he29-net/thermal-cam/3.Software/User/gd32f103c_lcd_eval.c

/*!
    \file    gd32f103c_lcd_eval.c
    \brief   LCD driver functions

    \version 2014-12-26, V1.0.0, demo for GD32F10x
    \version 2017-06-20, V2.0.0, demo for GD32F10x
    \version 2018-07-31, V2.1.0, demo for GD32F10x
*/

/*
    Copyright (c) 2018, GigaDevice Semiconductor Inc.

    All rights reserved.

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
    1. Redistributions of source code must retain the above copyright notice, this
       list of conditions and the following disclaimer.
    2. Redistributions in binary form must reproduce the above copyright notice,
       this list of conditions and the following disclaimer in the documentation
       and/or other materials provided with the distribution.
    3. Neither the name of the copyright holder nor the names of its contributors
       may be used to endorse or promote products derived from this software without
       specific prior written permission.

    THIS SOFTWARE IS PROVIDED BY THE COPYRIGHT HOLDERS AND CONTRIBUTORS "AS IS"
AND ANY EXPRESS OR IMPLIED WARRANTIES, INCLUDING, BUT NOT LIMITED TO, THE IMPLIED
WARRANTIES OF MERCHANTABILITY AND FITNESS FOR A PARTICULAR PURPOSE ARE DISCLAIMED.
IN NO EVENT SHALL THE COPYRIGHT HOLDER OR CONTRIBUTORS BE LIABLE FOR ANY DIRECT,
INDIRECT, INCIDENTAL, SPECIAL, EXEMPLARY, OR CONSEQUENTIAL DAMAGES (INCLUDING, BUT
NOT LIMITED TO, PROCUREMENT OF SUBSTITUTE GOODS OR SERVICES; LOSS OF USE, DATA, OR
PROFITS; OR BUSINESS INTERRUPTION) HOWEVER CAUSED AND ON ANY THEORY OF LIABILITY,
WHETHER IN CONTRACT, STRICT LIABILITY, OR TORT (INCLUDING NEGLIGENCE OR OTHERWISE)
ARISING IN ANY WAY OUT OF THE USE OF THIS SOFTWARE, EVEN IF ADVISED OF THE POSSIBILITY
OF SUCH DAMAGE.
*/

#include "gd32f103c_lcd_eval.h"
#include "16x8.h"

void exmc_lcd_init(void)
{
	ILI9341_BK_OFF;

	//时钟使能
    rcu_periph_clock_enable(RCU_AF);
	rcu_periph_clock_enable(RCU_GPIOA);
	rcu_periph_clock_enable(RCU_GPIOB);
	rcu_periph_clock_enable(RCU_GPIOC);
	rcu_periph_clock_enable(RCU_GPIOD);
	rcu_periph_clock_enable(RCU_GPIOE);

	//初始化
    gpio_init(ILI9341_CS_PORT, GPIO_MODE_OUT_PP, GPIO_OSPEED_50MHZ, ILI9341_CS_PIN);
	gpio_init(ILI9341_DC_PORT, GPIO_MODE_OUT_PP, GPIO_OSPEED_50MHZ, ILI9341_DC_PIN);
	gpio_init(ILI9341_WR_PORT, GPIO_MODE_OUT_PP, GPIO_OSPEED_50MHZ, ILI9341_WR_PIN);
	gpio_init(ILI9341_RD_PORT, GPIO_MODE_OUT_PP, GPIO_OSPEED_50MHZ, ILI9341_RD_PIN);
	gpio_init(ILI9341_BK_PORT, GPIO_MODE_OUT_PP, GPIO_OSPEED_50MHZ, ILI9341_BK_PIN);
	gpio_init(ILI9341_DATA_PORT, GPIO_MODE_OUT_PP, GPIO_OSPEED_50MHZ, ILI9341_DATA_PIN);
}

void ILI9341_Write_Cmd(uint16_t usCmd)
{
	ILI9341_CS_CLR;	// 开始片选	/ start chip select
	ILI9341_DC_CLR;	// 写命令	/ write command
	ILI9341_RD_SET;	// 禁止读	/ disable reading
	DATAOUT(usCmd);	// 输出命令	/ output command
	ILI9341_WR_CLR;	// 写入开始	/ start of write
	ILI9341_WR_SET;	// 写入结束	/ end of write
	ILI9341_CS_SET;	// 结束片选	/ end chip select
}


/**
  * @brief  从ILI9341读取数据
  * @param  无
  * @retval 读取到的数据
  */
uint16_t ILI9341_Read_Data(void)
{
	uint16_t data;
 	GPIO_CTL0(GPIOB) = 0x88888888;				// PB0-7  上拉输入
	GPIO_CTL1(GPIOB) = 0x88888888;				// PB8-15 上拉输入
	GPIO_OCTL(ILI9341_DATA_PORT) = 0x0000;		// 全部输出0

	ILI9341_DC_SET;
	ILI9341_WR_SET;

	ILI9341_CS_CLR;
	//读取数据
	ILI9341_RD_CLR;

	data=DATAIN;
	ILI9341_RD_SET;
	ILI9341_CS_SET;

	GPIO_CTL0(GPIOB) = 0x33333333; //PB0-7  上拉输出
	GPIO_CTL1(GPIOB) = 0x33333333; //PB8-15 上拉输出
	GPIO_OCTL(ILI9341_DATA_PORT) = 0xFFFF;    //全部输出高
	return data;
}


void lcd_init(void)
{
	/*  Power control B (CFh)  功耗控制B */
	delay_1ms(5);
	ILI9341_Write_Cmd(0xCF);
	ILI9341_Write_Data(0x00);
	ILI9341_Write_Data(0x81);
	ILI9341_Write_Data(0x30);

	/*  Power on sequence control (EDh) 电源序列控制 */
	delay_1ms(5);
	ILI9341_Write_Cmd(0xED);
	ILI9341_Write_Data(0x64);
	ILI9341_Write_Data(0x03);
	ILI9341_Write_Data(0x12);
	ILI9341_Write_Data(0x81);

	/*  Driver timing control A (E8h) 驱动时序控制A */
	delay_1ms(5);
	ILI9341_Write_Cmd(0xE8);
	ILI9341_Write_Data(0x85);
	ILI9341_Write_Data(0x10);
	ILI9341_Write_Data(0x78);

	/*  Power control A (CBh) 功耗控制A */
	delay_1ms(5);
	ILI9341_Write_Cmd(0xCB);
	ILI9341_Write_Data(0x39);
	ILI9341_Write_Data(0x2C);
	ILI9341_Write_Data(0x00);
	ILI9341_Write_Data(0x34);
	ILI9341_Write_Data(0x02);

	/* Pump ratio control (F7h) 泵比控制 */
	delay_1ms(5);
	ILI9341_Write_Cmd(0xF7);
	ILI9341_Write_Data(0x20);

	/* Driver timing control B 驱动时序控制B */
	delay_1ms(5);
	ILI9341_Write_Cmd(0xEA);
	ILI9341_Write_Data(0x00);
	ILI9341_Write_Data(0x00);

	/* Frame Rate Control (In Normal Mode/Full Colors) (B1h) 帧率控制 */
	delay_1ms(5);
	ILI9341_Write_Cmd(0xB1);
	ILI9341_Write_Data(0x00);  //内部时钟不分频
	ILI9341_Write_Data(0x1B);  //帧率为70Hz

	/*  Display Function Control (B6h) */
	delay_1ms(5);
	ILI9341_Write_Cmd(0xB6);
	ILI9341_Write_Data(0x0A);
	ILI9341_Write_Data(0xA2);

	/* Power Control 1 (C0h) */
	delay_1ms(5);
	ILI9341_Write_Cmd(0xC0);
	ILI9341_Write_Data(0x35);

	/* Power Control 2 (C1h) */
	delay_1ms(5);
	ILI9341_Write_Cmd(0xC1);
	ILI9341_Write_Data(0x11);

	/* VCOM Control 1(C5h) */
	ILI9341_Write_Cmd(0xC5);
	ILI9341_Write_Data(0x45);
	ILI9341_Write_Data(0x45);

	/*  VCOM Control 2(C7h)  */
	ILI9341_Write_Cmd(0xC7);
	ILI9341_Write_Data(0xA2);

	/* Enable 3G (F2h) */
	ILI9341_Write_Cmd(0xF2);
	ILI9341_Write_Data(0x00);

	/* Gamma Set (26h) */
	ILI9341_Write_Cmd(0x26);
	ILI9341_Write_Data(0x01);
	delay_1ms(5);

	/* Positive Gamma Correction */
	ILI9341_Write_Cmd(0xE0); //Set Gamma
	ILI9341_Write_Data(0x0F);
	ILI9341_Write_Data(0x26);
	ILI9341_Write_Data(0x24);
	ILI9341_Write_Data(0x0B);
	ILI9341_Write_Data(0x0E);
	ILI9341_Write_Data(0x09);
	ILI9341_Write_Data(0x54);
	ILI9341_Write_Data(0xA8);
	ILI9341_Write_Data(0x46);
	ILI9341_Write_Data(0x0C);
	ILI9341_Write_Data(0x17);
	ILI9341_Write_Data(0x09);
	ILI9341_Write_Data(0x0F);
	ILI9341_Write_Data(0x07);
	ILI9341_Write_Data(0x00);

	/* Negative Gamma Correction (E1h) */
	ILI9341_Write_Cmd(0xE1); //Set Gamma
	ILI9341_Write_Data(0x00);
	ILI9341_Write_Data(0x19);
	ILI9341_Write_Data(0x1B);
	ILI9341_Write_Data(0x04);
	ILI9341_Write_Data(0x10);
	ILI9341_Write_Data(0x07);
	ILI9341_Write_Data(0x2A);
	ILI9341_Write_Data(0x47);
	ILI9341_Write_Data(0x39);
	ILI9341_Write_Data(0x03);
	ILI9341_Write_Data(0x06);
	ILI9341_Write_Data(0x06);
	ILI9341_Write_Data(0x30);
	ILI9341_Write_Data(0x38);
	ILI9341_Write_Data(0x0F);

//	/* memory access control set 存储器访问控制 */
//	delay_1ms(5);
//	ILI9341_Write_Cmd(0x36);
//	ILI9341_Write_Data(0x68);
//	delay_1ms(5);

//	/* column address control set 列地址设置 */
//	ILI9341_Write_Cmd(0x2A);
//	ILI9341_Write_Data(0x00);
//	ILI9341_Write_Data(0x00);  //列开始地址  0
//	ILI9341_Write_Data(0x01);
//	ILI9341_Write_Data(0x3F);  //列结束地址  319
//
//	/* page address control set 行地址设置 */
//	delay_1ms(5);
//	ILI9341_Write_Cmd(0x2B);
//	ILI9341_Write_Data(0x00);
//	ILI9341_Write_Data(0x00);  //行开始地址  0
//	ILI9341_Write_Data(0x00);
//	ILI9341_Write_Data(0xEF);  //行结束地址  239

	/*  Pixel Format Set (3Ah)  */
	delay_1ms(5);
	ILI9341_Write_Cmd(0x3a);
	ILI9341_Write_Data(0x55);

	/* Sleep Out (11h)  退出睡眠模式 */
	ILI9341_Write_Cmd(0x11);
	delay_1ms(5);
	delay_1ms(5);

	/* Display ON (29h) 开显示 */
	ILI9341_Write_Cmd(0x29);

//	/* write gram start */
//	ILI9341_Write_Cmd(0x2C);
}


/* 设置液晶GRAM的扫描方向
 * 当设置成不同的扫描模式时, page(即x) 跟 column(即y) 的值是会改变的
 */
void Lcd_GramScan(void)
{
	ILI9341_Write_Cmd(0x36);
	ILI9341_Write_Data(0x68);	//68

	ILI9341_Write_Cmd(0x2A);
	ILI9341_Write_Data(0x00);
	ILI9341_Write_Data(0x00);
	ILI9341_Write_Data(0x01);
	ILI9341_Write_Data(0x3F);

	ILI9341_Write_Cmd(0x2B);
	ILI9341_Write_Data(0x00);
	ILI9341_Write_Data(0x00);
	ILI9341_Write_Data(0x00);
	ILI9341_Write_Data(0xEF);

	/* write gram start */
	ILI9341_Write_Cmd(0x2C);
}


//设置光标位置
//Xpos:横坐标
//Ypos:纵坐标
void LCD_SetCursor(uint16_t Xpos, uint16_t Ypos)
{
	ILI9341_Write_Cmd(0x2A);
	ILI9341_Write_Data(Xpos >> 8);
	ILI9341_Write_Data(Xpos & 0xFF);
	ILI9341_Write_Cmd(0x2B);
	ILI9341_Write_Data(Ypos >> 8);
	ILI9341_Write_Data(Ypos & 0xFF);
}


// 读取个某点的颜色值 / Read the color value of a certain point
// x, y : 坐标 / Coordinates
// 返回值:此点的颜色 / Return: color value

//uint16_t LCD_ReadPoint(uint16_t x, uint16_t y)
//{
// 	uint16_t r = 0, g = 0, b = 0;
//
//	LCD_SetCursor(x,y);
//	ILI9341_Write_Cmd(0x2E);	// 9341/6804/3510 发送读GRAM指令
//
// 	ILI9341_Read_Data();		// dummy Read
//	Delay_50ns(2);
// 	r = ILI9341_Read_Data();	// 实际坐标颜色

//	Delay_50ns(2);
//	b = ILI9341_Read_Data();
//	g = r & 0xFF;	       		// 对于9341/5310/5510,第一次读取的是RG的值,R在前,G在后,各占8位
//	g <<= 8;
//
//	return (((r >> 11) << 11) | ((g >> 10) << 5) | (b >> 11));	// ILI9341/NT35310/NT35510需要公式转换一下
//}

uint16_t LCD_ReadPoint(uint16_t x, uint16_t y)
{
 	uint16_t r = 0, g = 0, b = 0;

	LCD_SetCursor(x, y);
	ILI9341_Write_Cmd(0x2E);

 	GPIO_CTL0(GPIOB) = 0x88888888;				// PB0-7  上拉输入
	GPIO_CTL1(GPIOB) = 0x88888888;				// PB8-15 上拉输入
	GPIO_OCTL(ILI9341_DATA_PORT) = 0x0000;		// 全部输出0

	ILI9341_DC_SET;
	ILI9341_WR_SET;
	ILI9341_CS_CLR;
	ILI9341_RD_CLR;
	r = DATAIN;
	ILI9341_RD_SET;

	ILI9341_RD_CLR;
	r = DATAIN;
	ILI9341_RD_SET;

	ILI9341_RD_CLR;
	b = DATAIN;
	ILI9341_RD_SET;
	ILI9341_CS_SET;

	GPIO_CTL0(GPIOB) = 0x33333333;				// PB0-7  上拉输出
	GPIO_CTL1(GPIOB) = 0x33333333;				// PB8-15 上拉输出
	GPIO_OCTL(ILI9341_DATA_PORT) = 0xFFFF;		// 全部输出高

	g = r & 0xFF;		       //对于9341/5310/5510,第一次读取的是RG的值,R在前,G在后,各占8位
	g <<= 8;

	return (((r >> 11) << 11) | ((g >> 10) << 5) | (b >> 11));//ILI9341/NT35310/NT35510需要公式转换一下
}


//================================================================================================
//	实现功能：	设置窗口
//	输入参数：	x0,y0,x1,y1    x轴开始，y轴开始，x轴结束，y轴结束
//================================================================================================
void LCD_setwindow(unsigned int x0, unsigned int y0, unsigned int x1, unsigned int y1)
{
	ILI9341_Write_Cmd(0x2a);
	ILI9341_Write_Data(x0 >> 8);
	ILI9341_Write_Data(x0 & 0xff);
	ILI9341_Write_Data(x1 >> 8);
	ILI9341_Write_Data(x1 & 0xff);

	ILI9341_Write_Cmd(0x2b);
	ILI9341_Write_Data(y0 >> 8);
	ILI9341_Write_Data(y0 & 0xff);
	ILI9341_Write_Data(y1 >> 8);
	ILI9341_Write_Data(y1 & 0xff);

	ILI9341_Write_Cmd(0x2C);
}

//在指定区域内填充单个颜色
//(sx,sy),(ex,ey):填充矩形对角坐标,区域大小为:(ex-sx+1)*(ey-sy+1)
//color:要填充的颜色
void LCD_Fill(uint16_t sx, uint16_t sy, uint16_t ex, uint16_t ey, uint16_t color)
{
    unsigned int i, j;

 	LCD_setwindow(sx, sy, ex, ey);

	for (i = sy; i <= ey; i++)
	{
	    for (j = sx; j <= ex; j++)
		{
			ILI9341_Write_Data(color);
		}
	}
}

void LCD_Showchar(unsigned int x, unsigned int y,unsigned char c, unsigned int color, unsigned int b_color)
{
	unsigned int s_x ,s_y, temp;
  	unsigned int j;
  	c -= 32;

	LCD_setwindow(x, y, x + 7, y + 15);
	for (s_y = 0; s_y < 16; s_y++)
	{
	   j = c;
	   j = j * 16 + s_y;
	   temp = font16x8[j];
	   for (s_x = 0; s_x < 8; s_x++)
	   {
			if ((temp & (0x80 >> (s_x))) == (0x80 >> (s_x)))
			{
				ILI9341_Write_Data(color);
			}
			else
			{
				ILI9341_Write_Data(b_color);
			}
	   }
	}
}


// write text directly to the display (no transparency)
void LCD_ShowString(unsigned int x, unsigned int y, const char *s, unsigned int color, unsigned int b_color)
{
	while (*s != '\0')
	{
		LCD_Showchar(x, y, *s, color, b_color);
		x = x + 8;
		s++;
	}
}


/**********************************************************************************************************
*	函 数 名：Buf_Showchar
*	功能说明：Draws half a character with no background to the current display buffer strip.
*	形    参：
*	返 回 值：
**********************************************************************************************************/
void Buf_Showchar(unsigned int x, unsigned int y, unsigned char c, unsigned int color, uint8_t UpOrDn)
{
	unsigned int  s_x, s_y, temp;
	unsigned int j;
	c -= 32;

	if (UpOrDn == 0)		//上半部分 / draw the upper half
	{
		for (s_y = 0; s_y < 8; s_y++)
		{
			j = c;
			j = j * 16 + s_y;
			temp = font16x8[j];
			for (s_x = 0; s_x < 8; s_x++)
			{
				if ((temp & (0x80 >> s_x)) == (0x80 >> s_x))
					data.DisBuf[(s_y + y) * 320 + x + s_x] = color;
			}
		}
	}
	else if	(UpOrDn == 1)	//下半部分 / draw the lower half
	{
		for (s_y = 8; s_y < 16; s_y++)
		{
			j = c;
			j = j * 16 + s_y;
			temp = font16x8[j];
			for (s_x = 0; s_x < 8; s_x++)
			{
				if ((temp & (0x80 >> s_x)) == (0x80 >> s_x))
					data.DisBuf[(s_y - 8 + y) * 320 + x + s_x] = color;
			}
		}
	}
	else					// draw lower-case letters only (y tweaks the fit in the 10 line buffer)
	{
		for (s_y = 6 - y; s_y < 16 - y; s_y++)
		{
			j = c;
			j = j * 16 + s_y;
			temp = font16x8[j];
			for (s_x = 0; s_x < 8; s_x++)
			{
				if ((temp & (0x80 >> s_x)) == (0x80 >> s_x))
					data.DisBuf[(s_y - 6 + y) * 320 + x + s_x] = color;
			}
		}
	}
}


/**********************************************************************************************************
*	函 数 名：Buf_ShowString
*	功能说明：
*	形    参：
*	返 回 值：
**********************************************************************************************************/
void Buf_ShowString(unsigned int x, unsigned int y,const char *s, unsigned int color, uint8_t UpOrDn)
{
	while(*s != '\0')
	{
		Buf_Showchar(x, y, *s, color, UpOrDn);
		x = x + 8;
		s++;
	}
}


/**********************************************************************************************************
*	函 数 名：Buf_ShowNum
*	功能说明：显示数字，范围：-999~999
*	形    参：
*	返 回 值：
**********************************************************************************************************/
void Buf_ShowNum(unsigned int x, unsigned int y, int num, unsigned int color, uint8_t UpOrDn)
{
	if (num < 0)
	{
		num = -num;
		Buf_Showchar(x, y, '-', color, UpOrDn);
		x += 8;
	}

	if (num >= 100)
	{
		Buf_Showchar(x, y, num / 100 + '0', color, UpOrDn);
		Buf_Showchar(x + 8, y, (num / 10) % 10 + '0', color, UpOrDn);
		Buf_Showchar(x + 16, y, num % 10 + '0', color, UpOrDn);
	}
	else if (num >= 10)
	{
		Buf_Showchar(x, y, num / 10 + '0', color, UpOrDn);
		Buf_Showchar(x + 8, y, num % 10 + '0', color, UpOrDn);
	}
	else {
		Buf_Showchar(x, y, num + '0', color, UpOrDn);
	}
}


/**********************************************************************************************************
*	函 数 名：Buf_SmallFloatNum
*	功能说明：显示温度值，温度范围-40~300，温度值放大了10倍：-400~3000
*	形    参：
*	返 回 值：
**********************************************************************************************************/
void Buf_SmallFloatNum(int x, int y, int16_t num, unsigned int color, uint8_t UpOrDn, bool alignRight)
{
	if (num < 0)
	{
		num = -num;
		Buf_Showchar(x, y, '-', color, UpOrDn);
		x += 8;
	}

	if (num >= 1000)
	{
		Buf_Showchar(x, y, num / 1000 + '0', color, UpOrDn);
		x += 8;
		Buf_Showchar(x, y, (num / 100) % 10 + '0', color, UpOrDn);
		x += 8;
		Buf_Showchar(x, y, (num % 100) / 10 + '0', color, UpOrDn);
		x += 8;
		Buf_Showchar(x, y, '.', color, UpOrDn);
		x += 8;
		Buf_Showchar(x, y, num % 10 + '0', color, UpOrDn);
	}
    else if (num >= 100)
	{
		if (alignRight) x += 8;
		Buf_Showchar(x, y, num / 100 + '0', color, UpOrDn);
		x += 8;
		Buf_Showchar(x, y, (num / 10) % 10 + '0', color, UpOrDn);
		x += 8;
		Buf_Showchar(x, y, '.', color, UpOrDn);
		x += 8;
		Buf_Showchar(x, y, num % 10 + '0', color, UpOrDn);
	}
	else if (num >= 10)
	{
		if (alignRight) x += 16;
		Buf_Showchar(x, y, num / 10 + '0', color, UpOrDn);
		x += 8;
		Buf_Showchar(x, y, '.', color, UpOrDn);
		x += 8;
		Buf_Showchar(x, y, num % 10 + '0', color, UpOrDn);
	}
	else
	{
		if (alignRight) x += 24;
		Buf_Showchar(x, y, 0 + '0', color, UpOrDn);
		x += 8;
		Buf_Showchar(x, y, '.', color, UpOrDn);
		x += 8;
		Buf_Showchar(x, y, num + '0', color, UpOrDn);
	}

	x += 8;
	Buf_ShowString(x, y, "'C", color, UpOrDn);
}


// fill a rectangular area in the display buffer with selected color index
void Buf_Fill(uint16_t sx, uint16_t sy, uint16_t ex, uint16_t ey, uint8_t color)
{
    unsigned int i, j;

	for (i = sy; i <= ey; i++)
	{
	    for (j = sx; j <= ex; j++)
		{
			data.DisBuf[i * 320 + j] = color;
		}
	}
}


/**********************************************************************************************************
*	函 数 名：Disp_BatPower
*	功能说明：显示电量
*	形    参：
*	返 回 值：
**********************************************************************************************************/
void Disp_BatPower(void)
{
	uint16_t tmp;

	Buf_Fill( 6, 1,  6, 9, BUF_BLACK);	// left edge
	Buf_Fill(24, 1, 24, 9, BUF_BLACK);	// right edge
	Buf_Fill( 6, 1, 24, 1, BUF_BLACK);	// top edge
	Buf_Fill( 6, 9, 24, 9, BUF_BLACK);	// bottom edge
	Buf_Fill( 4, 4,  5, 6, BUF_BLACK);	// button

	// Measured battery voltages vs. ADCValue[0] * 660:
	// - 3.660 V = 560, 3.925 V = 600, 4.000 V = 611 → 0.00655 V per step, 0.001055 V per ADC step.
	// Interesting values:
	// - 660 = 4095 raw = 4.32 V seems to be the maximum / reference (only on USB power: measured 4.162 V = 659).
	// - 642 = 3983 raw = 4.20 V is considered as the maximum by the original code.
	// - 581 = 3602 raw = 3.80 V is considered as the maximum now (Li-ion voltage drops quickly at first, ignore it).
	// - 542 = 3365 raw = 3.55 V is considered empty battery (Li-ion could go lower, but 3.3 V reg may need a margin).
	const uint16_t min = 3365;
	const uint16_t max = 3602;
	if (CRG_STA_READ())		// 根据电量来显示竖杠 / Draw vertical bars based on battery voltage
	{
		tmp = ADCValue[0];
		if (tmp < min) tmp = min;
		else if (tmp > max) tmp = max;
		tmp = (tmp - min) * 17 / (max - min);
		if (tmp) Buf_Fill(24 - tmp, 2, 23, 8, BUF_WHITE);
		tmp = 17 - tmp;
		if (tmp) Buf_Fill(7, 2, 6 + tmp, 8, BUF_BLACK);
	}
	else					// 正在充电 / If battery is charging, draw a full green icon
	{
		Buf_Fill(7, 2, 23, 8, BUF_GREEN);
	}
}
