he29-net/thermal-cam/3.Software/User/MLX90640/headers/16x8.h

#ifndef __16x8_H
#define __16x8_H 	

/*16x8英文字符点阵数据文件*/
/*纵向取模*/

//包括以下字符的点阵数据：
//sp
//!"#$%&'()*+,-./
//0123456789
//:;<=>?@
//ABCDEFGHIJKLMNOPQRSTUVWXYZ
//[\]^_'
//abcdefghijklmnopqrstuvwxyz
//{|}~




const unsigned char font16x8[]={
/*                 sp                 */


0x00,0x00,0x00,0x00,0x00,0x00,0x00,0x00,0x00,0x00,0x00,0x00,0x00,0x00,0x00,0x00,



/*                 !"#$%&'()*+,-./                 */


/*--  文字:  !  --*/
/*--  宋体12;  此字体下对应的点阵为：宽x高=8x16   --*/
0x00,0x00,0x00,0x10,0x10,0x10,0x10,0x10,0x10,0x10,0x00,0x00,0x18,0x18,0x00,0x00,

/*--  文字:  "  --*/
/*--  宋体12;  此字体下对应的点阵为：宽x高=8x16   --*/
0x00,0x12,0x36,0x24,0x48,0x00,0x00,0x00,0x00,0x00,0x00,0x00,0x00,0x00,0x00,0x00,

/*--  文字:  #  --*/
/*--  宋体12;  此字体下对应的点阵为：宽x高=8x16   --*/
0x00,0x00,0x00,0x24,0x24,0x24,0xFE,0x48,0x48,0x48,0xFE,0x48,0x48,0x48,0x00,0x00,

/*--  文字:  $  --*/
/*--  宋体12;  此字体下对应的点阵为：宽x高=8x16   --*/
0x00,0x00,0x10,0x38,0x54,0x54,0x50,0x30,0x18,0x14,0x14,0x54,0x54,0x38,0x10,0x10,

/*--  文字:  %  --*/
/*--  宋体12;  此字体下对应的点阵为：宽x高=8x16   --*/
0x00,0x00,0x00,0x44,0xA4,0xA8,0xA8,0xA8,0x54,0x1A,0x2A,0x2A,0x2A,0x44,0x00,0x00,

/*--  文字:  &  --*/
/*--  宋体12;  此字体下对应的点阵为：宽x高=8x16   --*/
0x00,0x00,0x00,0x30,0x48,0x48,0x48,0x50,0x6E,0xA4,0x94,0x88,0x89,0x76,0x00,0x00,

/*--  文字:  '  --*/
/*--  宋体12;  此字体下对应的点阵为：宽x高=8x16   --*/
//0x00,0x60,0x60,0x20,0xC0,0x00,0x00,0x00,0x00,0x00,0x00,0x00,0x00,0x00,0x00,0x00,
0x00,0x0C,0x0C,0x00,0x00,0x00,0x00,0x00,0x00,0x00,0x00,0x00,0x00,0x00,0x00,0x00,

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
0x00,0x00,0x00,0x00,
//' '
0x00,0x00,0x00,0x00,0x00,0x00,0x00,0x00,0x00,0x00,0x00,0x00,0x00,0x00,0x00,0x00,
0x00,0x00,0x00,0x00,0x00,0x00,0x00,0x00,0x00,0x00,0x00,0x00,0x00,0x00,0x00,0x00,
0x00,0x00,0x00,0x00,0x00,0x00,0x00,0x00,0x00,0x00,0x00,0x00,0x00,0x00,0x00,0x00,
0x00,0x00,0x00,0x00,
//C
0x70,0x00,0xD8,0x00,0xD8,0x00,0xD8,0x00,0xD8,0x00,0x71,0xF0,0x07,0xFC,0x0F,0xFE,
0x1F,0xFE,0x1F,0x9F,0x1F,0x9F,0x1F,0x9F,0x1F,0x9F,0x1F,0x80,0x1F,0x80,0x1F,0x80,
0x1F,0x80,0x1F,0x9F,0x1F,0x9F,0x1F,0x9F,0x1F,0x9F,0x1F,0x9F,0x0F,0xFE,0x0F,0xFE,
0x07,0xFC,0x03,0xF0,
};



#endif
