he29-net/thermal-cam/3.Software/USB/msc_core.c

/*!
    \file  msc_core.c
    \brief USB MSC device class core functions

    \version 2014-12-26, V1.0.0, demo for GD32F10x
    \version 2017-06-20, V2.0.0, demo for GD32F10x
    \version 2018-07-31, V2.1.0, demo for GD32F10x
*/

/*
    Copyright (c) 2018, GigaDevice Semiconductor Inc.

    All rights reserved.

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
    1. Redistributions of source code must retain the above copyright notice, this 
       list of conditions and the following disclaimer.
    2. Redistributions in binary form must reproduce the above copyright notice, 
       this list of conditions and the following disclaimer in the documentation 
       and/or other materials provided with the distribution.
    3. Neither the name of the copyright holder nor the names of its contributors 
       may be used to endorse or promote products derived from this software without 
       specific prior written permission.

    THIS SOFTWARE IS PROVIDED BY THE COPYRIGHT HOLDERS AND CONTRIBUTORS "AS IS" 
AND ANY EXPRESS OR IMPLIED WARRANTIES, INCLUDING, BUT NOT LIMITED TO, THE IMPLIED 
WARRANTIES OF MERCHANTABILITY AND FITNESS FOR A PARTICULAR PURPOSE ARE DISCLAIMED. 
IN NO EVENT SHALL THE COPYRIGHT HOLDER OR CONTRIBUTORS BE LIABLE FOR ANY DIRECT, 
INDIRECT, INCIDENTAL, SPECIAL, EXEMPLARY, OR CONSEQUENTIAL DAMAGES (INCLUDING, BUT 
NOT LIMITED TO, PROCUREMENT OF SUBSTITUTE GOODS OR SERVICES; LOSS OF USE, DATA, OR 
PROFITS; OR BUSINESS INTERRUPTION) HOWEVER CAUSED AND ON ANY THEORY OF LIABILITY, 
WHETHER IN CONTRACT, STRICT LIABILITY, OR TORT (INCLUDING NEGLIGENCE OR OTHERWISE) 
ARISING IN ANY WAY OUT OF THE USE OF THIS SOFTWARE, EVEN IF ADVISED OF THE POSSIBILITY 
OF SUCH DAMAGE.
*/

#include "msc_core.h"
#include "usbd_std.h"
#include "bbb_scsi_driver.h"
#include "flash_access.h"
#include "usbd_int.h"

#define USBD_VID                     0x28E9
#define USBD_PID                     0x0285

extern bbb_cbw_struct bbb_cbw;
extern bbb_csw_struct bbb_csw;
extern uint8_t g_bbb_transport_stage;

static uint8_t usbd_msc_maxlun = 0;
static uint8_t usbd_msc_altset = 0;

usbd_int_cb_struct *usbd_int_fops = NULL;

/* note: it should use the C99 standard when compiling the below codes */
/* USB standard device descriptor */
const usb_descriptor_device_struct device_descripter =
{
    .Header ={.bLength = USB_DEVICE_DESC_SIZE, .bDescriptorType = USB_DESCTYPE_DEVICE},
    .bcdUSB = 0x0200,
    .bDeviceClass = 0x00,
    .bDeviceSubClass = 0x00,
    .bDeviceProtocol = 0x00,
    .bMaxPacketSize0 = USBD_EP0_MAX_SIZE,
    .idVendor = USBD_VID,
    .idProduct = USBD_PID,
    .bcdDevice = 0x0100,
    .iManufacturer = USBD_MFC_STR_IDX,
    .iProduct = USBD_PRODUCT_STR_IDX,
    .iSerialNumber = USBD_SERIAL_STR_IDX,
    .bNumberConfigurations = USBD_CFG_MAX_NUM
};

/* USB device configuration descriptor */
usb_descriptor_configuration_set_struct configuration_descriptor = 
{
    .Config = 
    {
        .Header = {.bLength = sizeof(usb_descriptor_configuration_struct), .bDescriptorType = USB_DESCTYPE_CONFIGURATION},
        .wTotalLength = USB_MSC_CONFIG_DESC_SIZE,
        .bNumInterfaces = 0x01,
        .bConfigurationValue = 0x01,
        .iConfiguration = 0x04,
        .bmAttributes = 0xC0,
        .bMaxPower = 0x32
    },
    .MSC_Interface = 
    {
        .Header = {.bLength = sizeof(usb_descriptor_interface_struct), .bDescriptorType = USB_DESCTYPE_INTERFACE},
        .bInterfaceNumber = 0x00,
        .bAlternateSetting = 0x00,
        .bNumEndpoints = 0x02,
        .bInterfaceClass = 0x08,
        .bInterfaceSubClass = 0x06,
        .bInterfaceProtocol = 0x50,
        .iInterface = 0x00
    },
    .MSC_INEndpoint = 
    {
        .Header = {.bLength = sizeof(usb_descriptor_endpoint_struct), .bDescriptorType = USB_DESCTYPE_ENDPOINT},
        .bEndpointAddress = MSC_IN_EP,
        .bmAttributes = 0x02,
        .wMaxPacketSize = MSC_EPIN_SIZE,
        .bInterval = 0x00
    },
    .MSC_OUTEndpoint = 
    {
        .Header = {.bLength = sizeof(usb_descriptor_endpoint_struct), .bDescriptorType = USB_DESCTYPE_ENDPOINT},
        .bEndpointAddress = MSC_OUT_EP,
        .bmAttributes = 0x02,
        .wMaxPacketSize = MSC_EPOUT_SIZE,
        .bInterval = 0x00
    }
};

/* USB language ID descriptor */
const usb_descriptor_language_id_struct usbd_language_id_desc = 
{
    .Header = 
     {
         .bLength = sizeof(usb_descriptor_language_id_struct), 
         .bDescriptorType = USB_DESCTYPE_STRING
     },
    .wLANGID = ENG_LANGID
};

/* usb string descriptor */
void *const usbd_strings[] = 
{
    [USBD_LANGID_STR_IDX] = (uint8_t *)&usbd_language_id_desc,
    [USBD_MFC_STR_IDX] = USBD_STRING_DESC("GigaDevice"),
    [USBD_PRODUCT_STR_IDX] = USBD_STRING_DESC("GD32 USB MSC in FS Mode"),
    [USBD_SERIAL_STR_IDX] = USBD_STRING_DESC("GD32F30X-V3.0.0-3a4b5ec")
};

/*!
    \brief      initialize the MSC device
    \param[in]  pudev: pointer to USB device instance
    \param[in]  config_index: configuration index
    \param[out] none
    \retval     USB device operation status
*/
usbd_status_enum msc_init (void *pudev, uint8_t config_index)
{
    /* initialize Tx endpoint */
    usbd_ep_init(pudev, ENDP_SNG_BUF, &(configuration_descriptor.MSC_INEndpoint));

    /* initialize Rx endpoint */
    usbd_ep_init(pudev, ENDP_SNG_BUF, &(configuration_descriptor.MSC_OUTEndpoint));

    flash_init();
  
    g_bbb_transport_stage = COMMAND_STAGE;
    /* prepare endpoint to receive first bbb_cbw */
    usbd_ep_rx (pudev,MSC_OUT_EP,(uint8_t *)&bbb_cbw, BBB_CBW_LENGTH);

    return USBD_OK;

}

/*!
    \brief      de-initialize the MSC device
    \param[in]  pudev: pointer to USB device instance
    \param[in]  config_index: configuration index
    \param[out] none
    \retval     USB device operation status
*/
usbd_status_enum  msc_deinit (void *pudev, uint8_t config_index)
{
    /* deinitialize MSC endpoints */
    usbd_ep_deinit (pudev, MSC_IN_EP);
    usbd_ep_deinit (pudev, MSC_OUT_EP);
   
    g_bbb_transport_stage = COMMAND_STAGE;
    /* prepare endpoint to receive first bbb_cbw */
    usbd_ep_rx (pudev,MSC_OUT_EP,(uint8_t *)&bbb_cbw, BBB_CBW_LENGTH);
  
    return USBD_OK;
}

/*!
    \brief      handle the MSC class-specific and standard requests
    \param[in]  pudev: pointer to USB device instance
    \param[in]  req: device class-specific request
    \param[out] none
    \retval     USB device operation status
*/
usbd_status_enum msc_req_handler (void *pudev, usb_device_req_struct *req)
{
    switch (req->bmRequestType & USB_REQ_MASK) {
    case USB_CLASS_REQ:
        switch (req->bRequest) {
        case BBB_GET_MAX_LUN:
            usbd_msc_maxlun = STORAGE_LUN_NUM - 1;
            g_bbb_transport_stage = COMMAND_STAGE;
            usbd_ep_tx (pudev, EP0_IN, (uint8_t *)&usbd_msc_maxlun, 1);
            break;
        case BBB_RESET :
            g_bbb_transport_stage = COMMAND_STAGE;
            /* prepare endpoint to receive first bbb_cbw */
            usbd_ep_rx (pudev, MSC_OUT_EP, (uint8_t *)&bbb_cbw, BBB_CBW_LENGTH);
            break;
        default:
            usbd_enum_error(pudev, req);
            return USBD_FAIL; 
        }
        break;
    case USB_STANDARD_REQ:
        /* standard device request */
        switch(req->bRequest) {
        case USBREQ_GET_INTERFACE:
            usbd_ep_tx (pudev, EP0_IN, (uint8_t *)&usbd_msc_altset, 1);
            break;
        case USBREQ_SET_INTERFACE:
            usbd_msc_altset = (uint8_t)(req->wValue);
            break;
        case USBREQ_CLEAR_FEATURE:
            usbd_ep_stall(pudev, MSC_IN_EP);
            
            break;
        default:
            break;
        }
    default:
        break;
    }

    return USBD_OK;
}

/*!
    \brief      handle data stage
    \param[in]  pudev: pointer to USB device instance
    \param[in]  rx_tx: the flag of Rx or Tx
    \param[in]  ep_id: the endpoint ID
    \param[out] none
    \retval     USB device operation status
*/
usbd_status_enum  msc_data_handler (void *pudev, usbd_dir_enum rx_tx, uint8_t ep_id)
{
    if ((USBD_TX == rx_tx) && ((MSC_IN_EP & 0x7F) == ep_id)) {
        if(COMMAND_STAGE != g_bbb_transport_stage){
            process_scsi_command(pudev); 
        }
        return USBD_OK;
        
    } else if ((USBD_RX == rx_tx) && ((MSC_OUT_EP & 0x7F) == ep_id)) {
        if(COMMAND_STAGE == g_bbb_transport_stage){
            scsi_command_parse();
            process_scsi_command(pudev);
        }else if(DATA_OUT_STAGE == g_bbb_transport_stage){
            process_scsi_command(pudev); 
        }
        return USBD_OK;
    }
    return USBD_FAIL;
}
