he29-net/thermal-cam/3.Software/User/Temp-adc.c

#include "Temp-adc.h"

uint32_t ADCValue[2];

/**********************************************************************************************************
*	函 数 名：ADC_DMA_Init
*	功能说明：ADC初始化
*	形    参：
*	返 回 值：
**********************************************************************************************************/ 
void ADC_DMA_Init(void)
{
	dma_parameter_struct dma_data_parameter;
	
    /* enable GPIOA clock */
    rcu_periph_clock_enable(RCU_GPIOA);
    /* enable ADC clock */
    rcu_periph_clock_enable(RCU_ADC0);
    /* enable DMA0 clock */
    rcu_periph_clock_enable(RCU_DMA0);
    /* config ADC clock */
    rcu_adc_clock_config(RCU_CKADC_CKAPB2_DIV8);
	
    /* config the GPIO as analog mode */
    gpio_init(GPIOA, GPIO_MODE_AIN, GPIO_OSPEED_50MHZ, GPIO_PIN_0|GPIO_PIN_1);	
	
    /* ADC DMA_channel configuration */
    dma_deinit(DMA0, DMA_CH0);    
    /* initialize DMA single data mode */
    dma_data_parameter.periph_addr  = (uint32_t)(&ADC_RDATA(ADC0));
    dma_data_parameter.periph_inc   = DMA_PERIPH_INCREASE_DISABLE;
    dma_data_parameter.memory_addr  = (uint32_t)(ADCValue);
    dma_data_parameter.memory_inc   = DMA_MEMORY_INCREASE_ENABLE;
    dma_data_parameter.periph_width = DMA_PERIPHERAL_WIDTH_32BIT;
    dma_data_parameter.memory_width = DMA_MEMORY_WIDTH_32BIT;  
    dma_data_parameter.direction    = DMA_PERIPHERAL_TO_MEMORY;
    dma_data_parameter.number       = 2;
    dma_data_parameter.priority     = DMA_PRIORITY_HIGH;
    dma_init(DMA0, DMA_CH0, &dma_data_parameter);
    dma_circulation_enable(DMA0, DMA_CH0);
    /* enable DMA channel */
    dma_channel_enable(DMA0, DMA_CH0);	

    /* reset ADC */
    adc_deinit(ADC0);
    /* ADC mode config */
    adc_mode_config(ADC_MODE_FREE); //ADC_DAUL_REGULAL_PARALLEL
    /* ADC contineous function enable */
    adc_special_function_config(ADC0, ADC_CONTINUOUS_MODE, ENABLE);
    /* ADC scan mode disable */
    adc_special_function_config(ADC0, ADC_SCAN_MODE, ENABLE);
    /* ADC data alignment config */
    adc_data_alignment_config(ADC0, ADC_DATAALIGN_RIGHT);
    /* ADC channel length config */
    adc_channel_length_config(ADC0, ADC_REGULAR_CHANNEL, 2);
 
    /* ADC regular channel config */
    adc_regular_channel_config(ADC0, 0, ADC_CHANNEL_0, ADC_SAMPLETIME_55POINT5);
    adc_regular_channel_config(ADC0, 1, ADC_CHANNEL_1, ADC_SAMPLETIME_55POINT5);	
    /* ADC trigger config */
    adc_external_trigger_source_config(ADC0, ADC_REGULAR_CHANNEL, ADC0_1_2_EXTTRIG_REGULAR_NONE);
    adc_external_trigger_config(ADC0, ADC_REGULAR_CHANNEL, ENABLE);
    
    /* enable ADC interface */
    adc_enable(ADC0);
    delay_1ms(1);
    /* ADC calibration and reset calibration */
    adc_calibration_enable(ADC0);

    /* ADC DMA function enable */
    adc_dma_mode_enable(ADC0);
    /* ADC software trigger enable */
    adc_software_trigger_enable(ADC0, ADC_REGULAR_CHANNEL);
}

/**********************************************************************************************************
*	函 数 名：OverTemp_Detect
*	功能说明：过温检测函数
*	形    参：
*	返 回 值：
**********************************************************************************************************/
void OverTemp_Detect(void)  //LM35，0.01V=1度
{

}
