he29-net/thermal-cam/3.Software/User/bsp.h

#ifndef __BSP_H
#define	__BSP_H

#include "gd32f10x.h"
#include "systick.h"
#include "GPIO.h"
#include "TIM.h"
#include "gd32f103c_lcd_eval.h"
#include <stdio.h>
#include "Temp-adc.h"
#include "MLX90640_API.h"
#include "MLX90640_I2C_Driver.h"
#include "MLX90640.h"
#include "usbd_std.h"
#include "msc_core.h"
#include "gd25qxx.h"
#include <string.h>
#include "diskio.h"
#include "ff.h"
#include "bmp.h"
#include "config.h"

typedef union{
	uint16_t mlx90640_Zoom10[834];  
	uint8_t  DisBuf[10*320];
	uint8_t  SPI_FLASH_BUF[4096];
} UnionData;

typedef union{
	uint16_t mlx90640To[768];
	uint16_t databuf[640];  
	uint8_t  bbb_data[MSC_MEDIA_PACKET_SIZE];
} UnionData2;

void rcu_config(void);
void gpio_config(void);
void nvic_config(void);

extern UnionData data;
extern UnionData2 data2;

extern const char *menu_text;
extern uint8_t menu_tweak;
extern const char *menu_value;

extern uint16_t *camColors;
extern int16_t range_low;
extern int16_t range_high;

#ifdef PROFILE
extern int16_t sensor_diff;
#endif

#endif
